petercsauer/ros_controller/Hardware/Panels/middle panel 1.SLDPRT

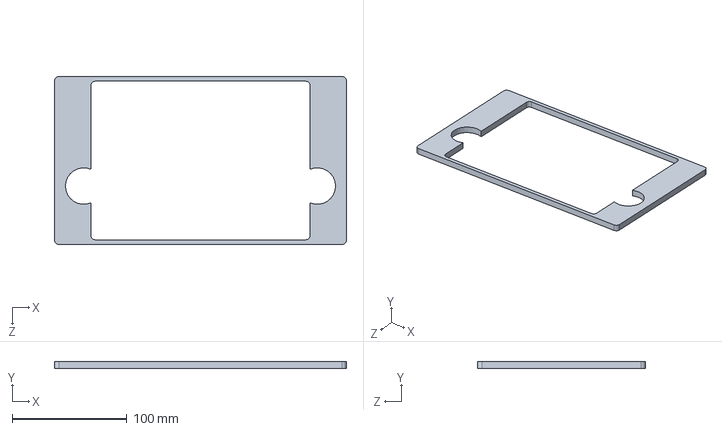
[picture p21: CAD file, 2021-03-16]
Hardware/Panels/middle panel 1.SLDPRT
254.0 x 6.35 x 146.1 mm
