petercsauer/ros_controller/Hardware/Electronics/HDMI Driver Board.SLDPRT

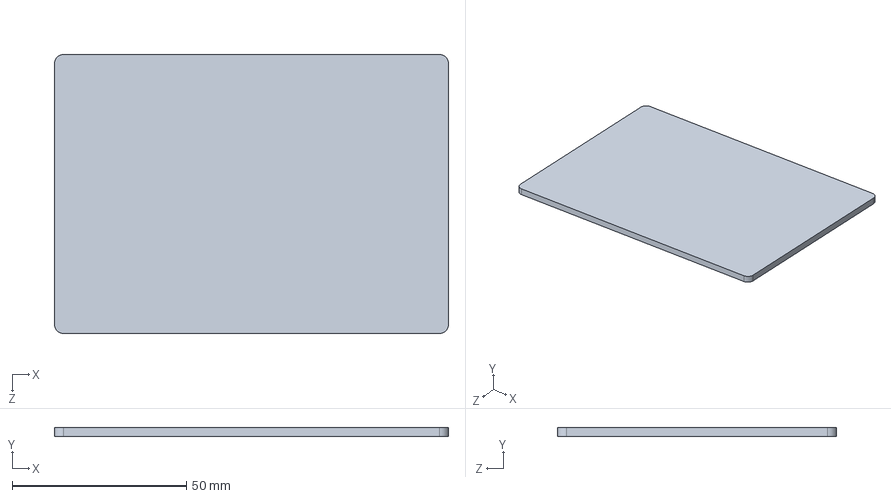
[picture p22: CAD file, 2021-03-16]
Hardware/Electronics/HDMI Driver Board.SLDPRT
113.0 x 2.54 x 80.0 mm
