petercsauer/ros_controller/Hardware/Panels/front panel.SLDPRT

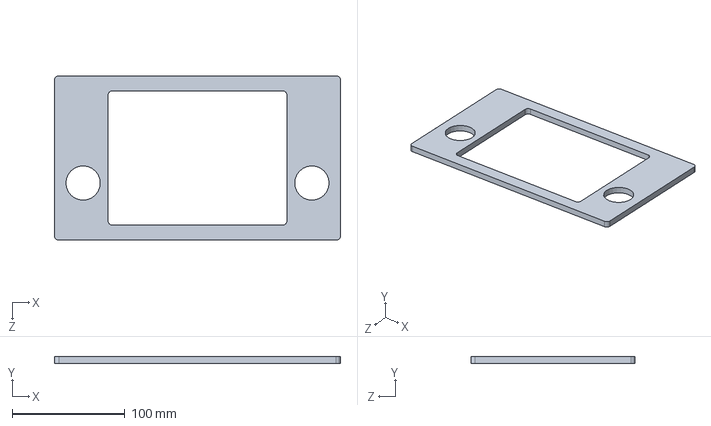
[picture p23: CAD file, 2021-03-16]
Hardware/Panels/front panel.SLDPRT
254.0 x 6.35 x 146.1 mm
