petercsauer/ros_controller/Hardware/Electronics/joystick-breakout.SLDPRT

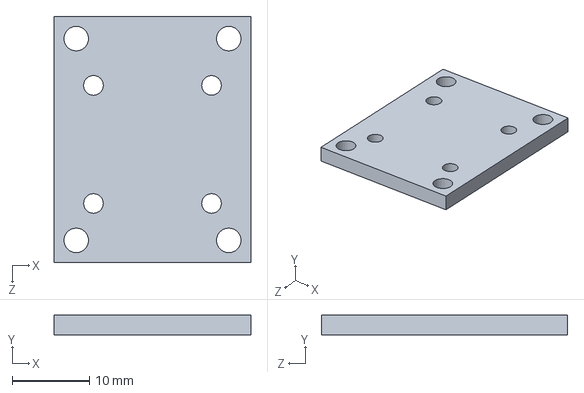
[picture p24: CAD file, 2021-03-16]
Hardware/Electronics/joystick-breakout.SLDPRT
25.4 x 2.54 x 31.8 mm
