petercsauer/ros_controller/Hardware/Electronics/SAINSMART NANO V3.0 ATMEGA328.SLDPRT

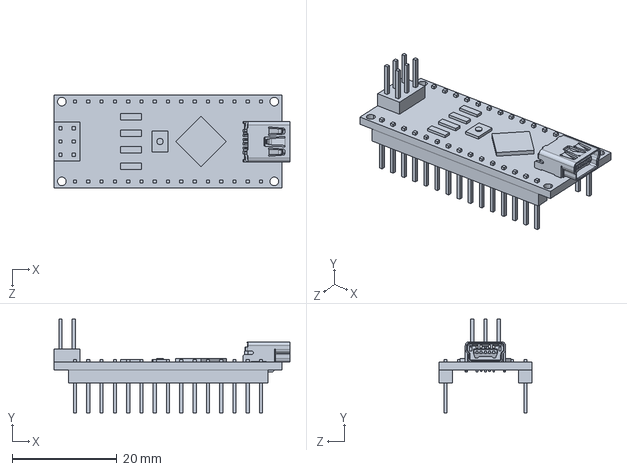
[picture p25: CAD file, 2021-03-16]
Hardware/Electronics/SAINSMART NANO V3.0 ATMEGA328.SLDPRT
45.1 x 18.0 x 17.8 mm
